espinr/activioty/docs/images/controller/newcheckpoint.gif

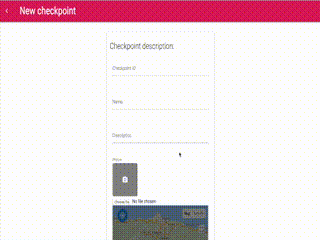
docs/images/controller/newcheckpoint.gif
