espinr/activioty/docs/images/controller/newrace.gif

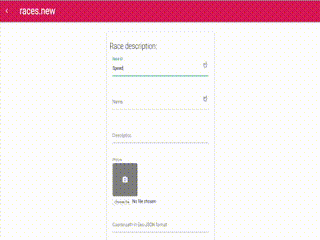
docs/images/controller/newrace.gif
