espinr/activioty/docs/images/controller/startlist.gif

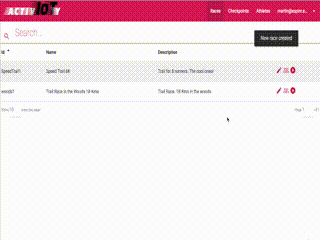
docs/images/controller/startlist.gif
