espinr/activioty/docs/images/implementation/arduino-raspberry.jpg

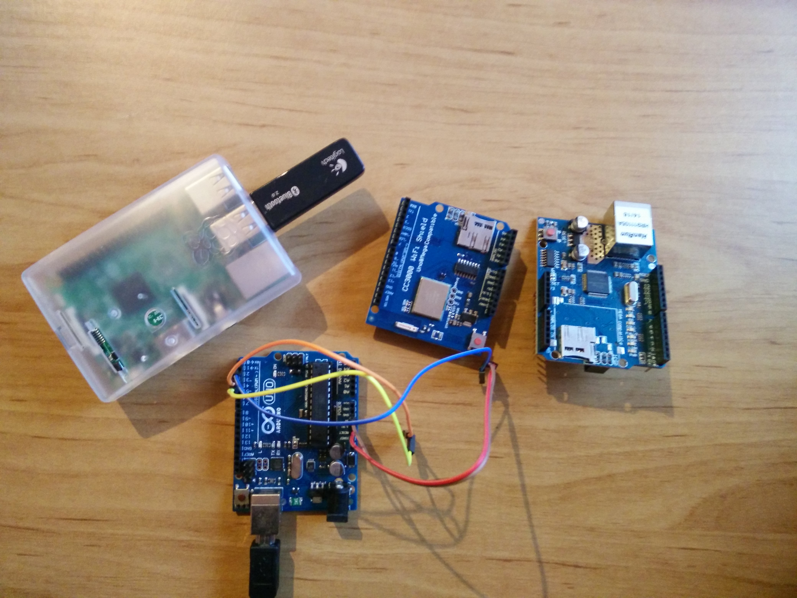
docs/images/implementation/arduino-raspberry.jpg
