espinr/activioty/docs/images/implementation/raspberry-pi.jpg

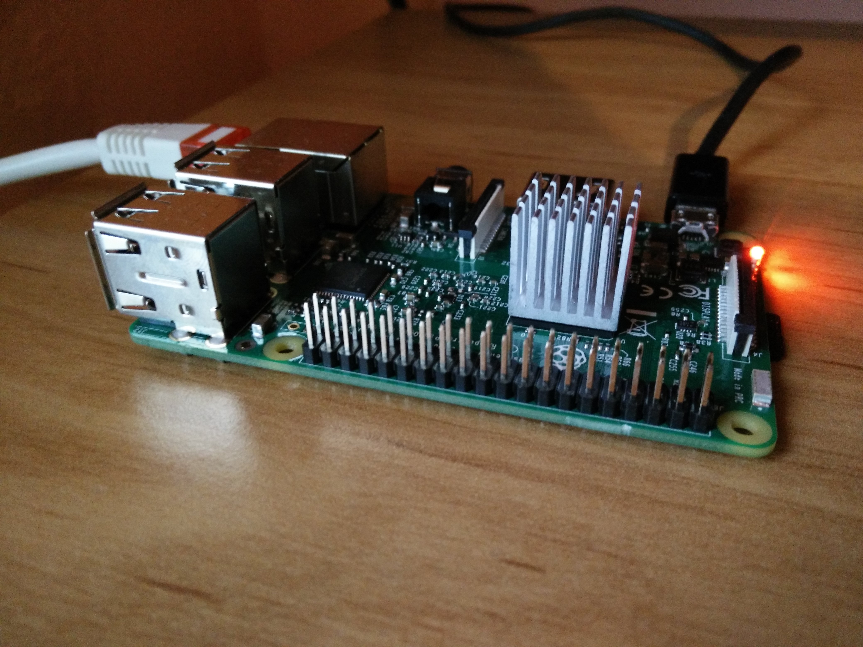
docs/images/implementation/raspberry-pi.jpg
