espinr/activioty/docs/images/implementation/rfid_reader_case_2.jpg

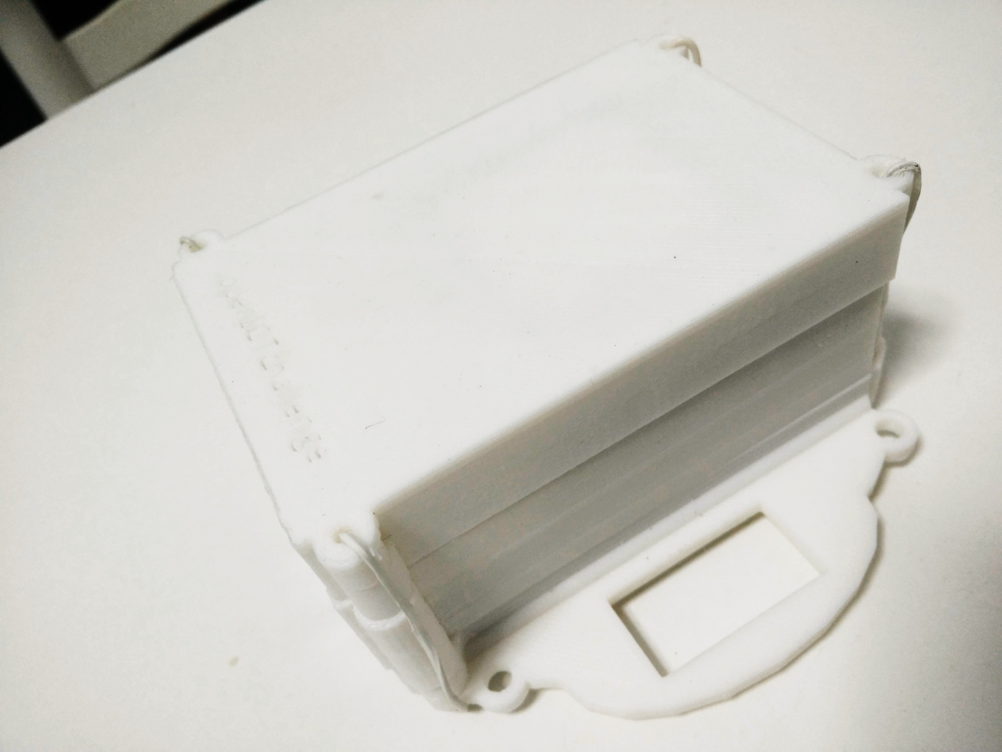
docs/images/implementation/rfid_reader_case_2.jpg
