espinr/activioty/docs/images/implementation/rfid_reader_case_3.jpg

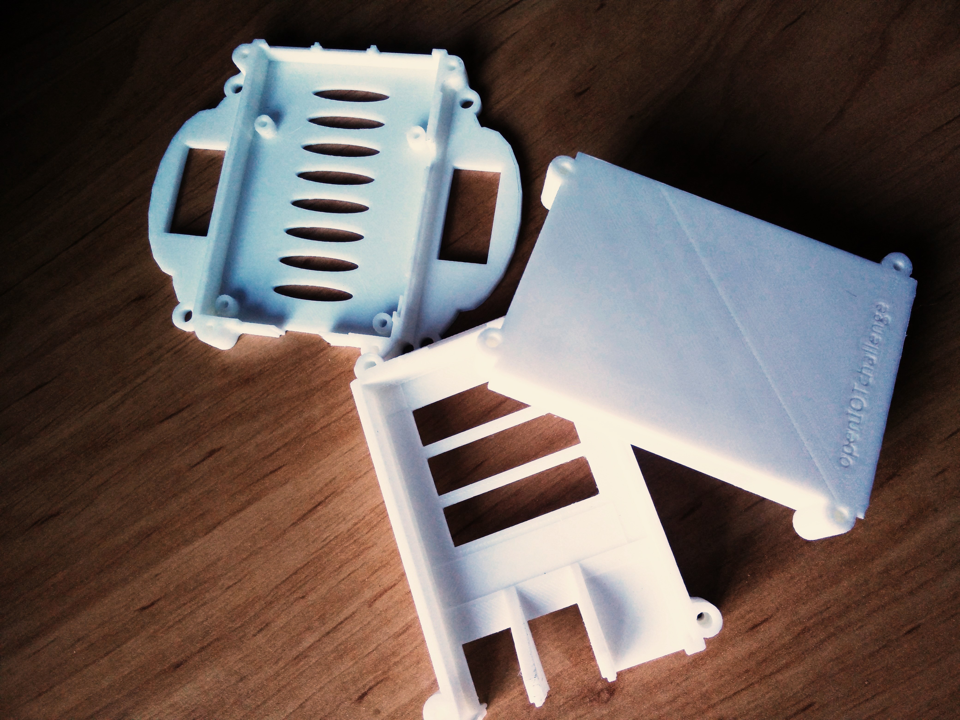
docs/images/implementation/rfid_reader_case_3.jpg
