espinr/activioty/docs/images/implementation/rfid_reader_case_closed.jpg

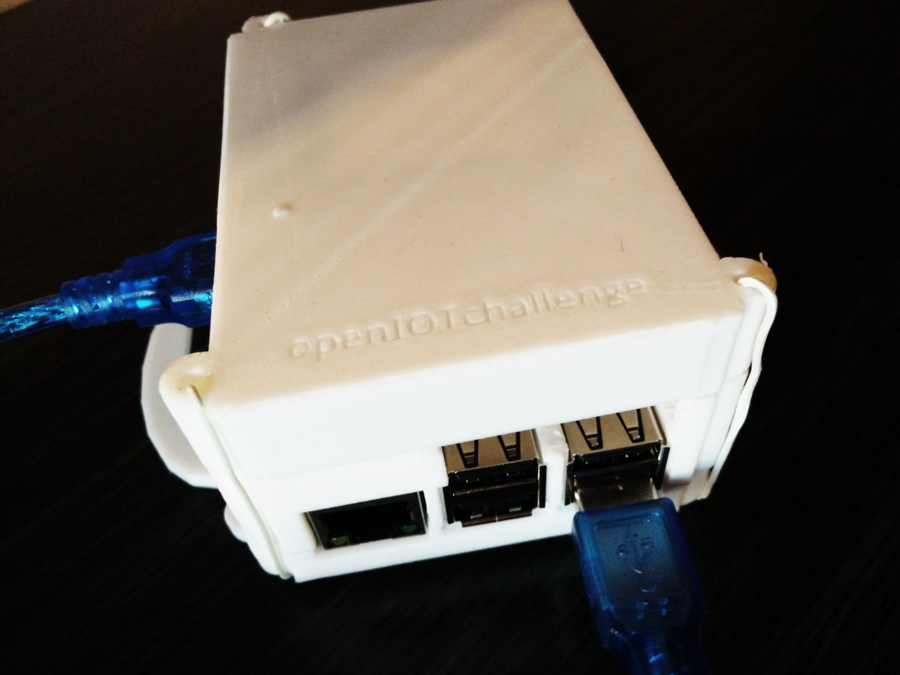
docs/images/implementation/rfid_reader_case_closed.jpg
