espinr/activioty/docs/images/implementation/rfid_reader_case_closed_2.jpg

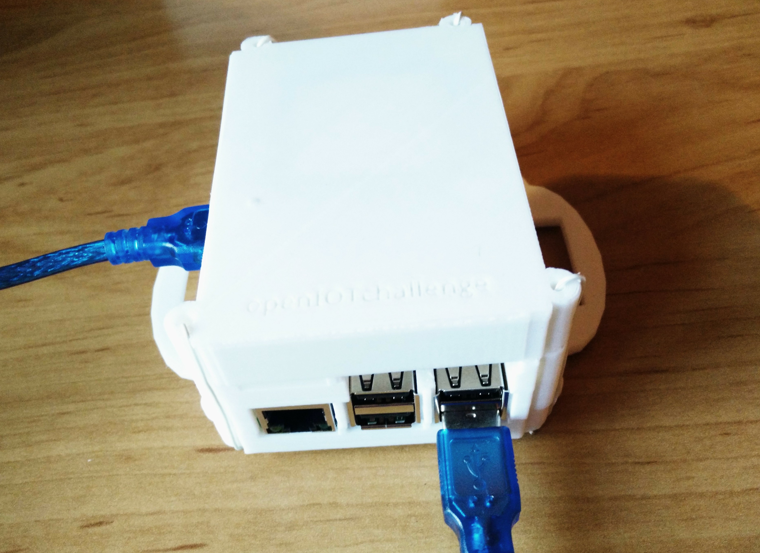
docs/images/implementation/rfid_reader_case_closed_2.jpg
