espinr/activioty/docs/images/implementation/rfid_reader_case_mounting.jpg

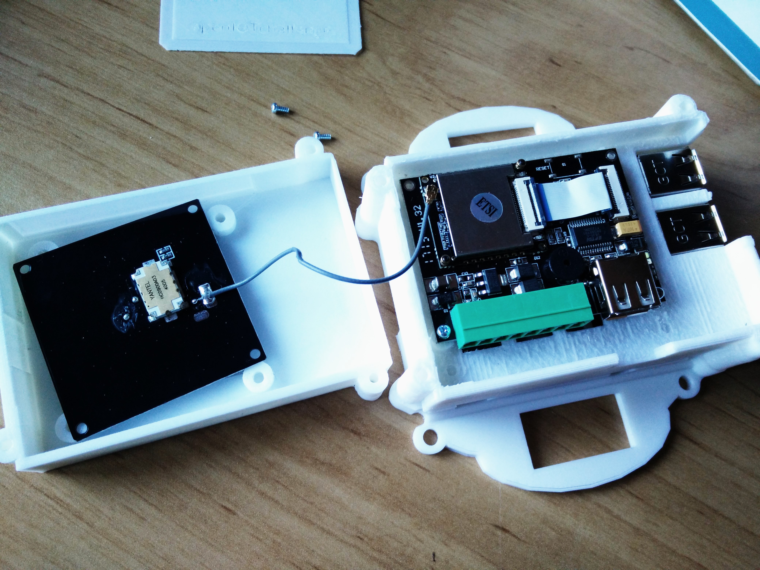
docs/images/implementation/rfid_reader_case_mounting.jpg
