espinr/activioty/docs/images/implementation/rfid_reader_case_open2.jpg

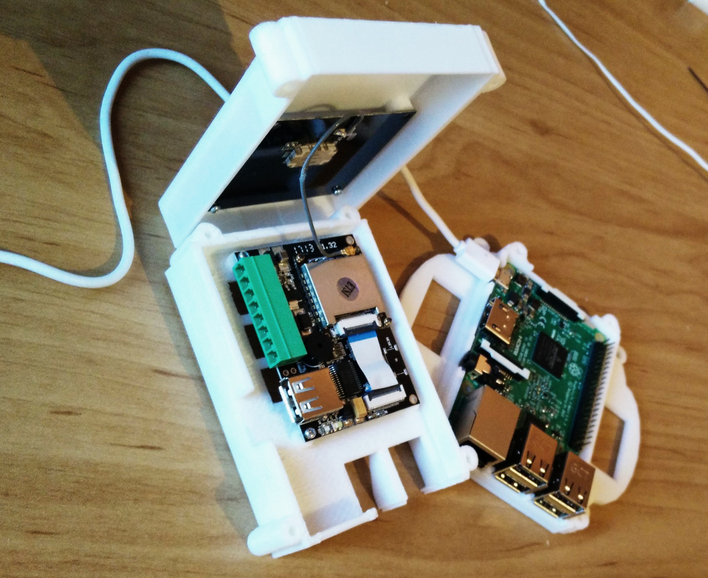
docs/images/implementation/rfid_reader_case_open2.jpg
