espinr/activioty/docs/images/implementation/rfid_reader_case_open.jpg

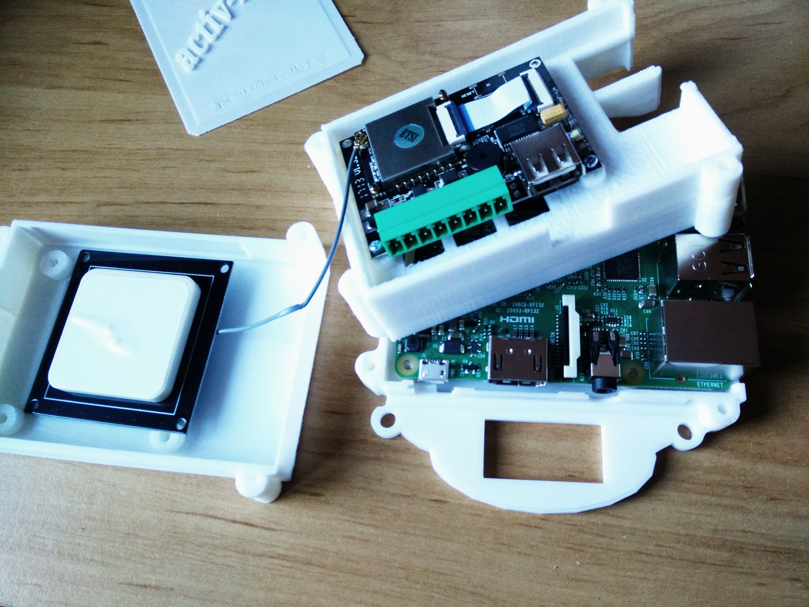
docs/images/implementation/rfid_reader_case_open.jpg
