espinr/activioty/docs/images/implementation/rfid_reader_case_raspberry.jpg

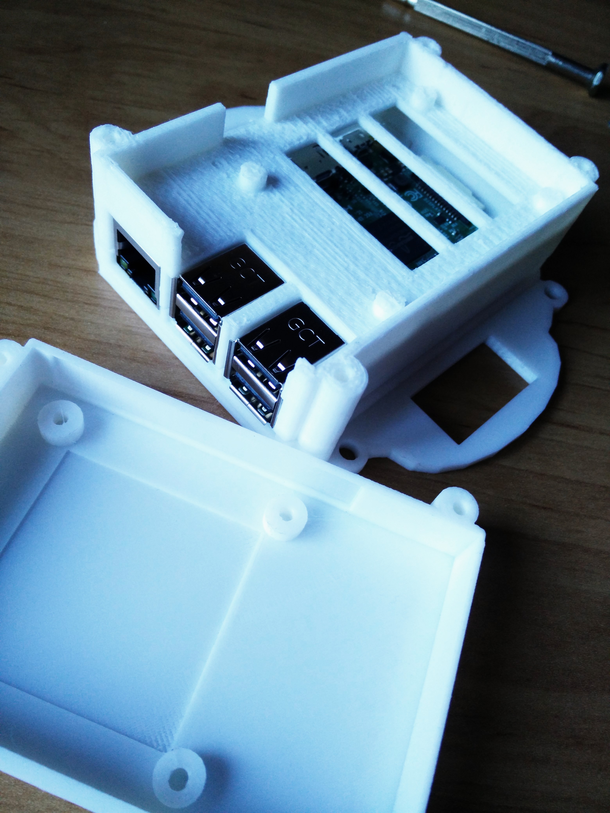
docs/images/implementation/rfid_reader_case_raspberry.jpg
