espinr/activioty/docs/images/implementation/rfid_reader_ready.jpg

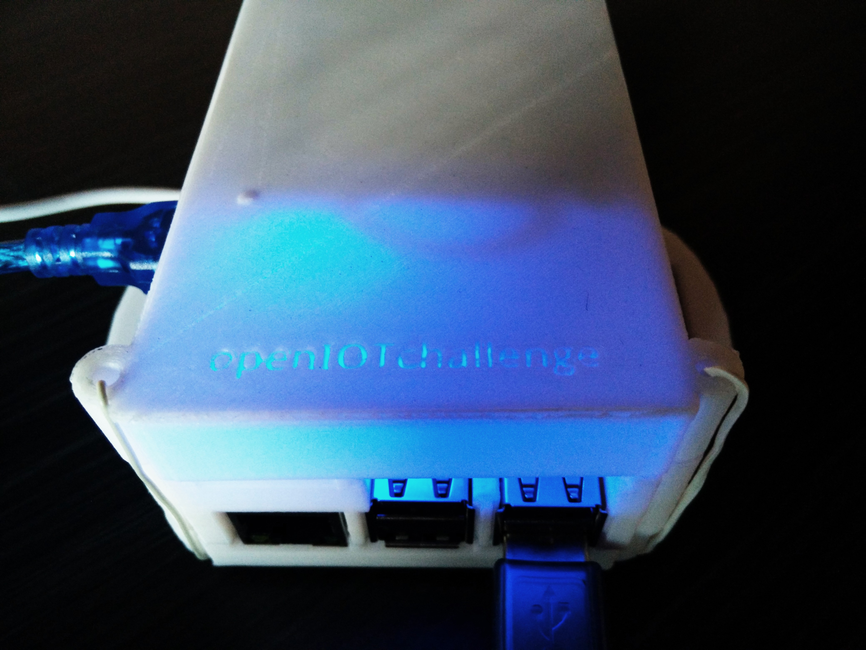
docs/images/implementation/rfid_reader_ready.jpg
