espinr/activioty/docs/images/implementation/tags_bib_numbers.jpg

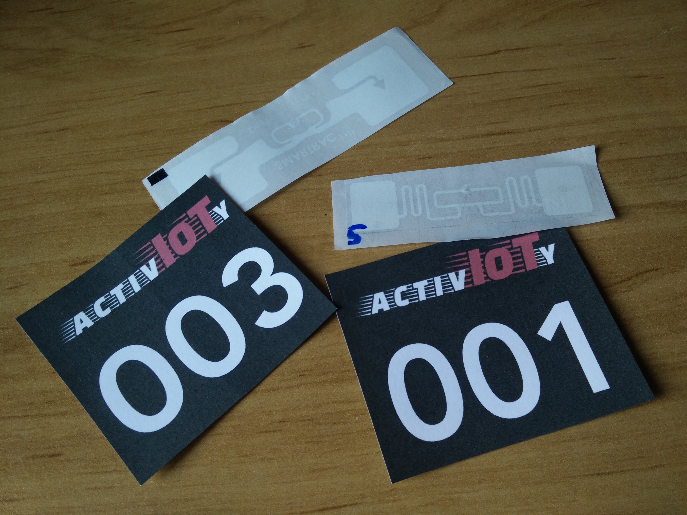
docs/images/implementation/tags_bib_numbers.jpg
