espinr/activioty/docs/images/implementation/tags_bib_numbers_1.jpg

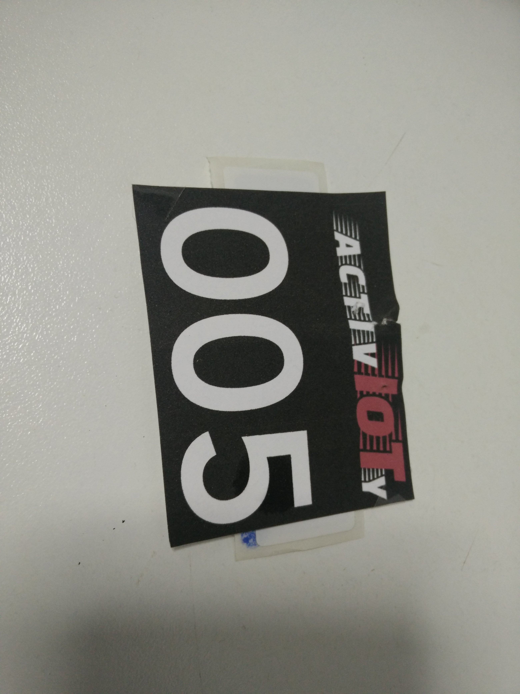
docs/images/implementation/tags_bib_numbers_1.jpg
