espinr/activioty/docs/images/implementation/upsquared2.jpg

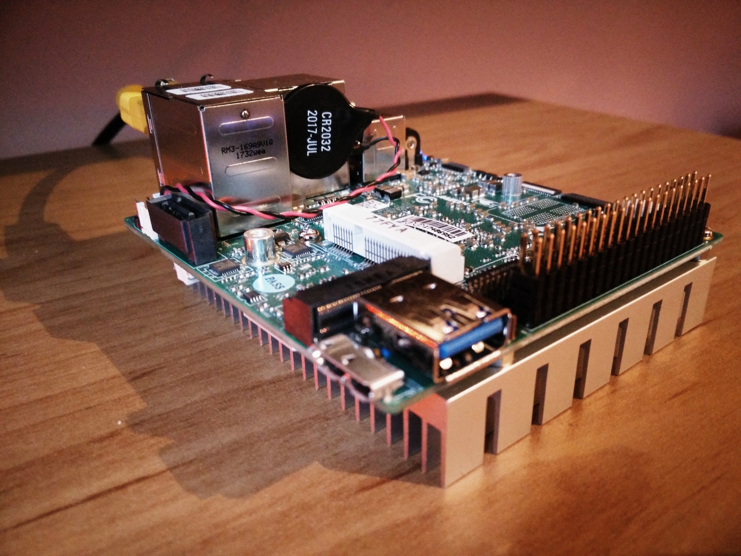
docs/images/implementation/upsquared2.jpg
