espinr/activioty/docs/images/implementation/workbench.jpg

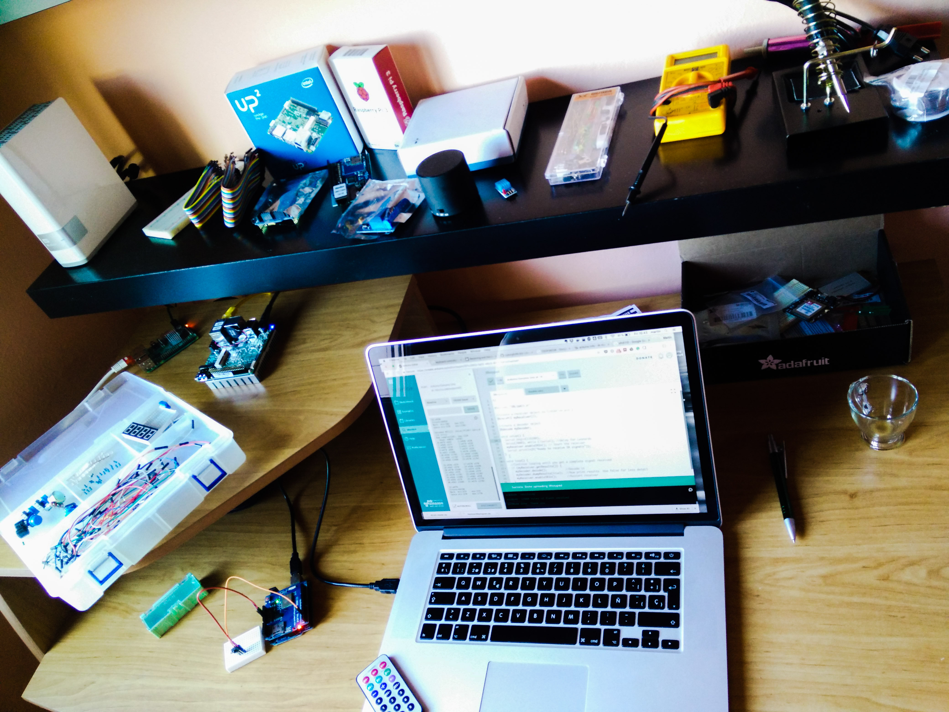
docs/images/implementation/workbench.jpg
