espinr/activioty/docs/images/components/checkpoints.png

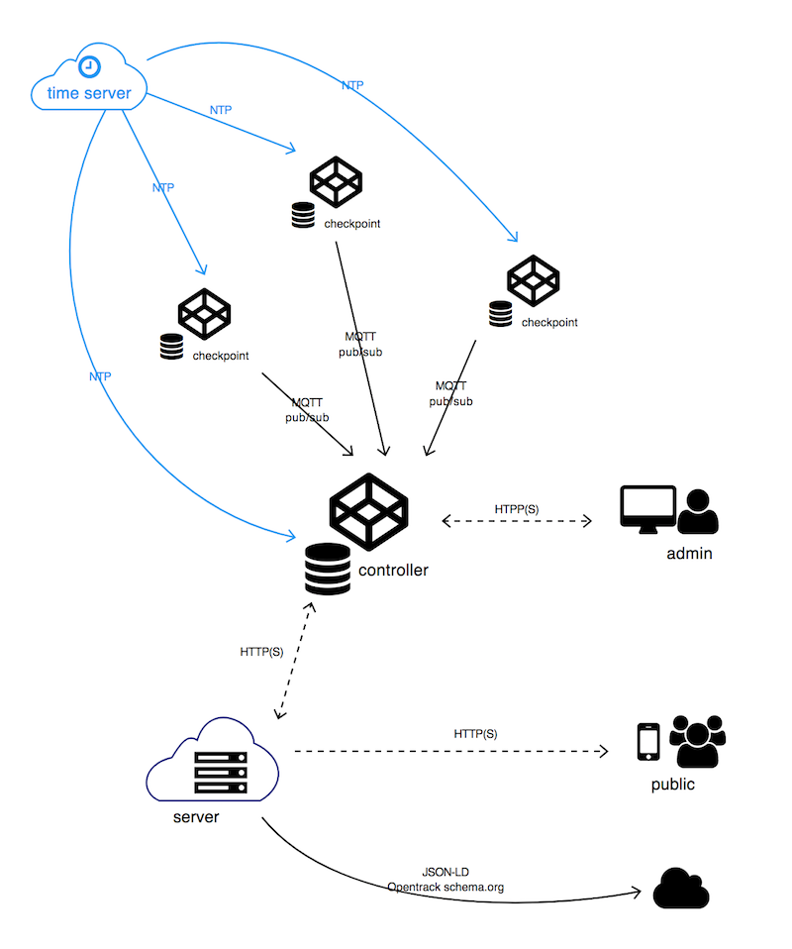
docs/images/components/checkpoints.png
